JoaoFilipeResende/Master-Thesis/Mechanical Parts/cilider_camara.SLDPRT

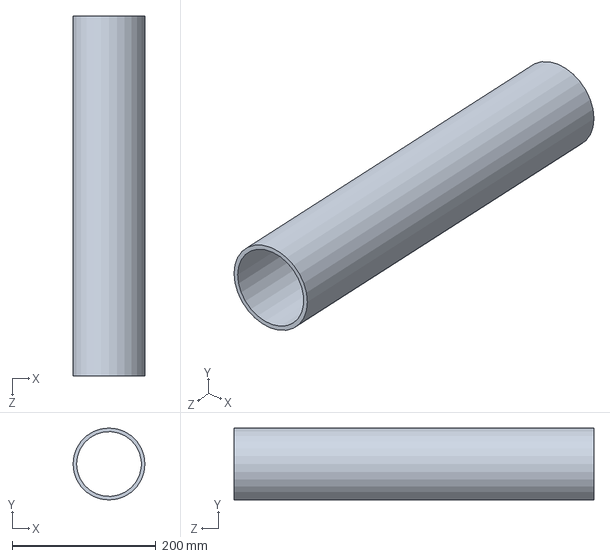
[picture p30: CAD file, 2022-01-28]
Mechanical Parts/cilider_camara.SLDPRT
100.0 x 100.0 x 500.0 mm
