JoaoFilipeResende/Master-Thesis/Mechanical Parts/tampa_back_camara.SLDPRT

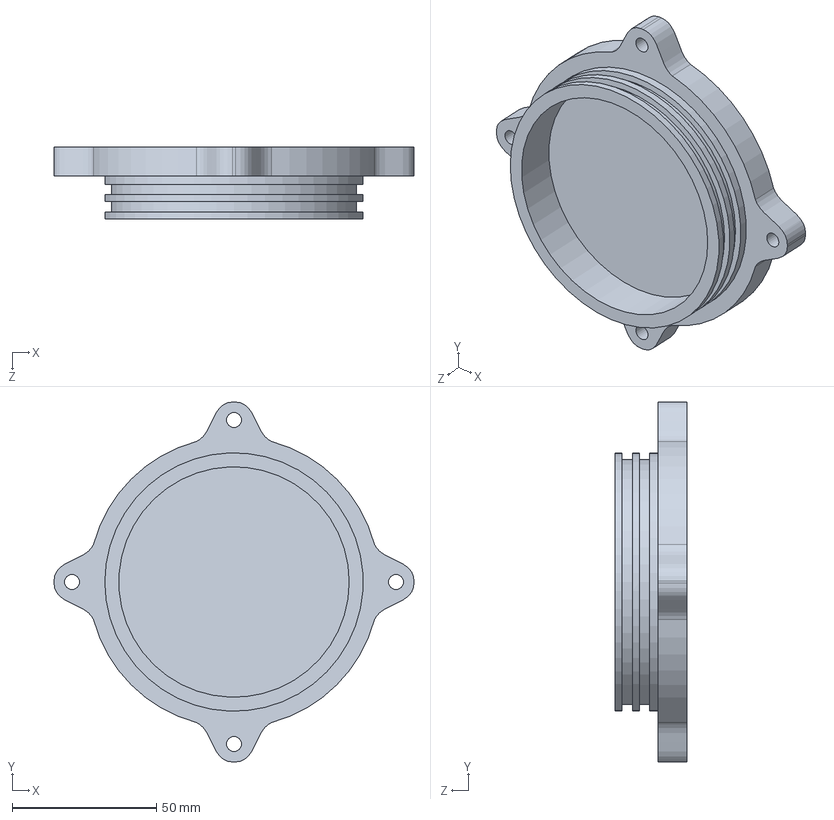
[picture p31: CAD file, 2022-01-28]
Mechanical Parts/tampa_back_camara.SLDPRT
125.0 x 125.0 x 25.0 mm
