JoaoFilipeResende/Master-Thesis/Mechanical Parts/mcbh8f-wb.SLDPRT

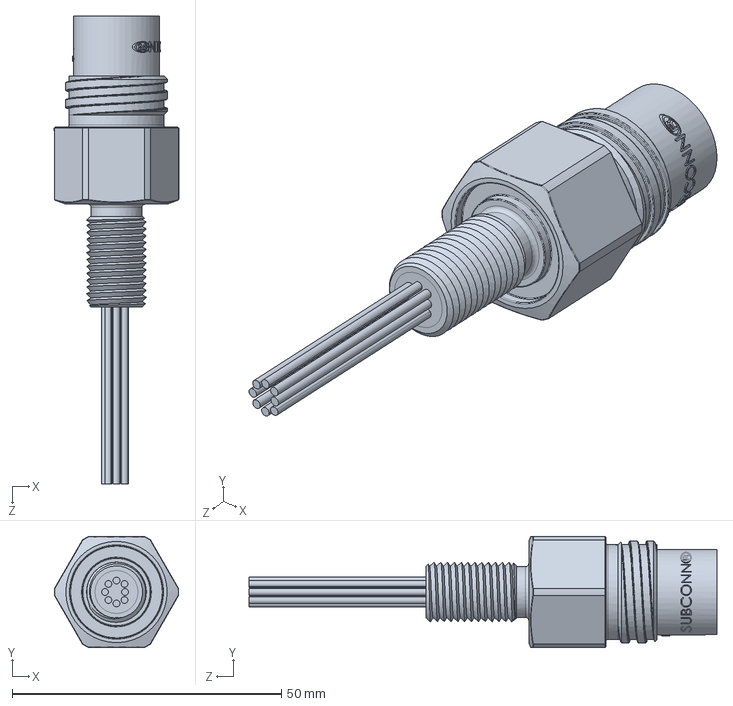
[picture p32: CAD file, 2022-01-28]
Mechanical Parts/mcbh8f-wb.SLDPRT
23.1 x 20.6 x 86.9 mm
