JoaoFilipeResende/Master-Thesis/Mechanical Parts/espacador.SLDPRT

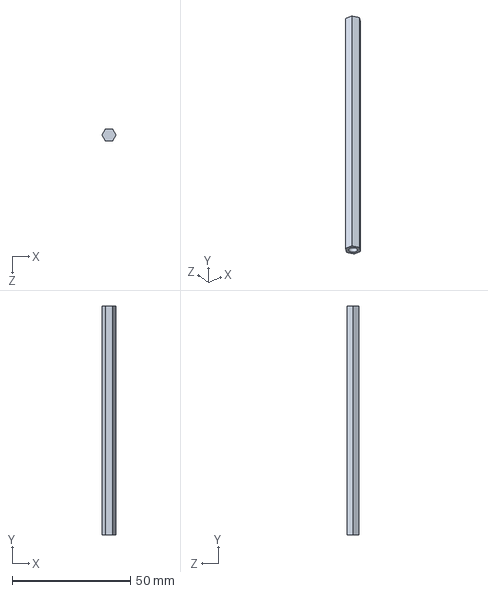
[picture p33: CAD file, 2022-01-28]
Mechanical Parts/espacador.SLDPRT
6.00 x 97.0 x 5.20 mm
