JoaoFilipeResende/Master-Thesis/Mechanical Parts/espacador_2.SLDPRT

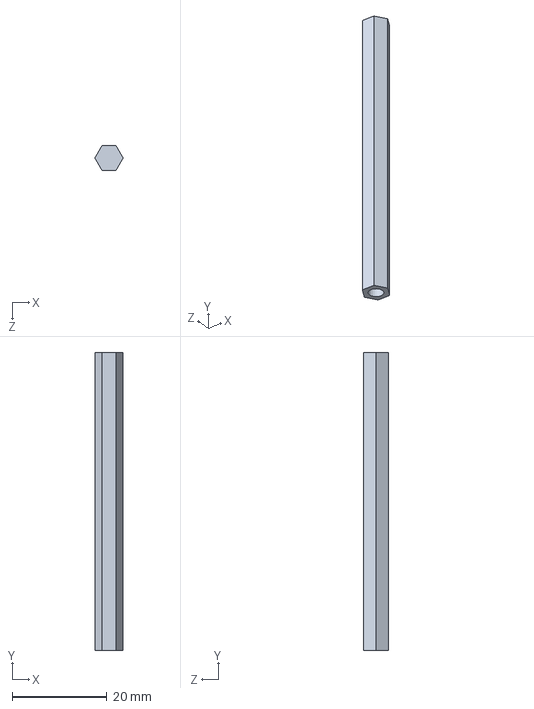
[picture p34: CAD file, 2022-01-28]
Mechanical Parts/espacador_2.SLDPRT
6.00 x 63.0 x 5.20 mm
