JoaoFilipeResende/Master-Thesis/Mechanical Parts/DTCM230-36.SLDPRT

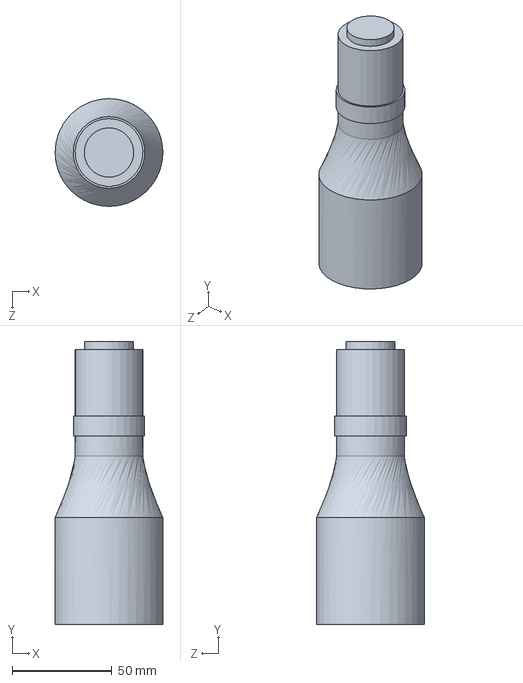
[picture p35: CAD file, 2022-01-28]
Mechanical Parts/DTCM230-36.SLDPRT
54.0 x 141.9 x 54.0 mm
