JoaoFilipeResende/Master-Thesis/Mechanical Parts/camara.SLDPRT

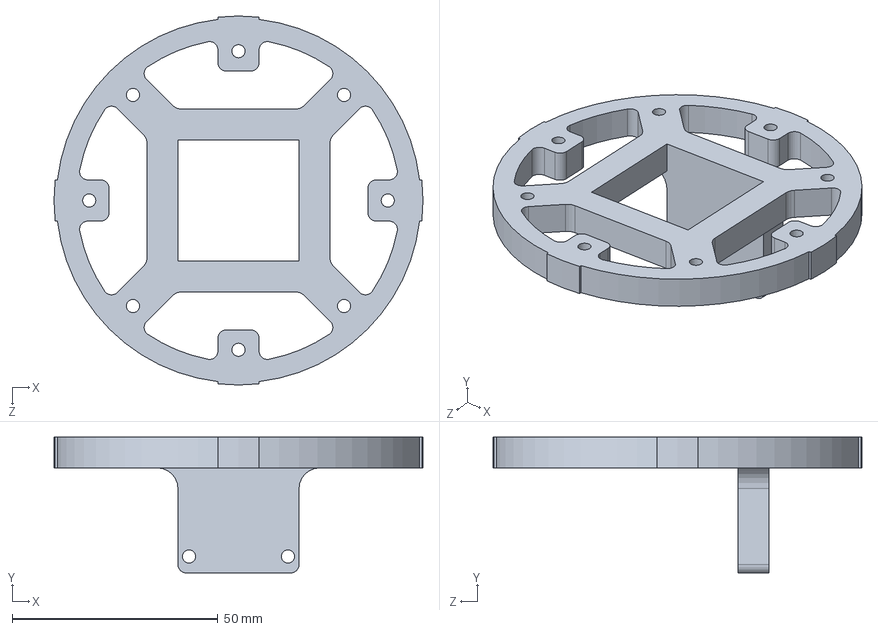
[picture p36: CAD file, 2022-01-28]
Mechanical Parts/camara.SLDPRT
89.6 x 33.0 x 89.6 mm
