JoaoFilipeResende/Master-Thesis/Mechanical Parts/suporte_lente_meio.SLDPRT

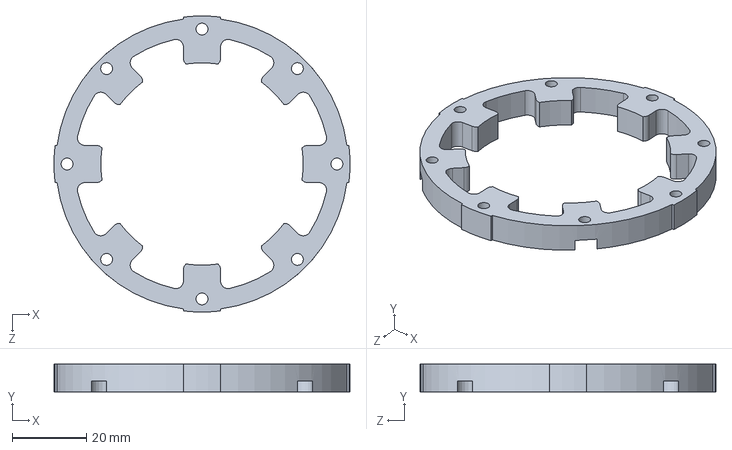
[picture p37: CAD file, 2022-01-28]
Mechanical Parts/suporte_lente_meio.SLDPRT
79.5 x 7.50 x 79.5 mm
