JoaoFilipeResende/Master-Thesis/Mechanical Parts/vara_suporte_camara.SLDPRT

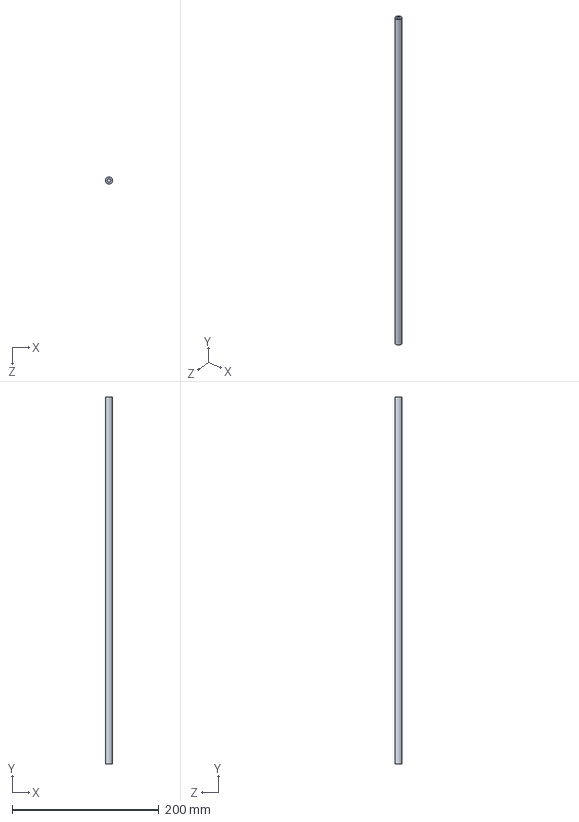
[picture p38: CAD file, 2022-01-28]
Mechanical Parts/vara_suporte_camara.SLDPRT
10.0 x 500.0 x 10.0 mm
