JoaoFilipeResende/Master-Thesis/Mechanical Parts/battery_sup.SLDPRT

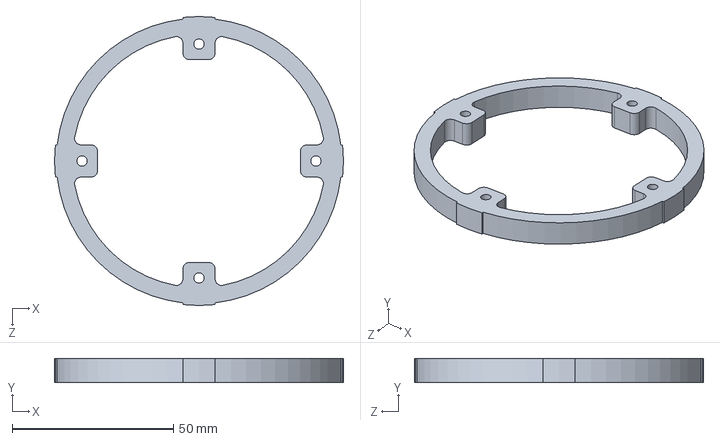
[picture p39: CAD file, 2022-01-28]
Mechanical Parts/battery_sup.SLDPRT
89.6 x 7.50 x 89.6 mm
