JoaoFilipeResende/Master-Thesis/Mechanical Parts/meio.SLDPRT

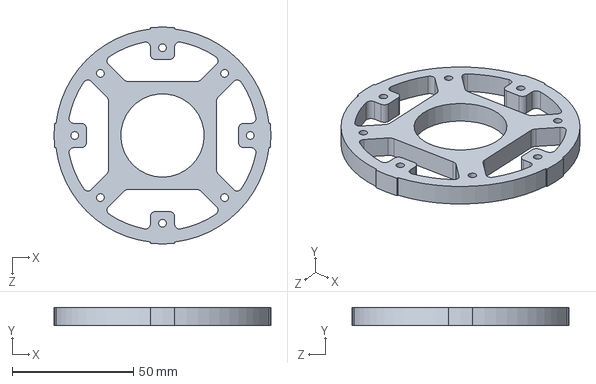
[picture p40: CAD file, 2022-01-28]
Mechanical Parts/meio.SLDPRT
89.6 x 7.50 x 89.6 mm
