JoaoFilipeResende/Master-Thesis/Mechanical Parts/tampa_front2_camara_light.SLDPRT

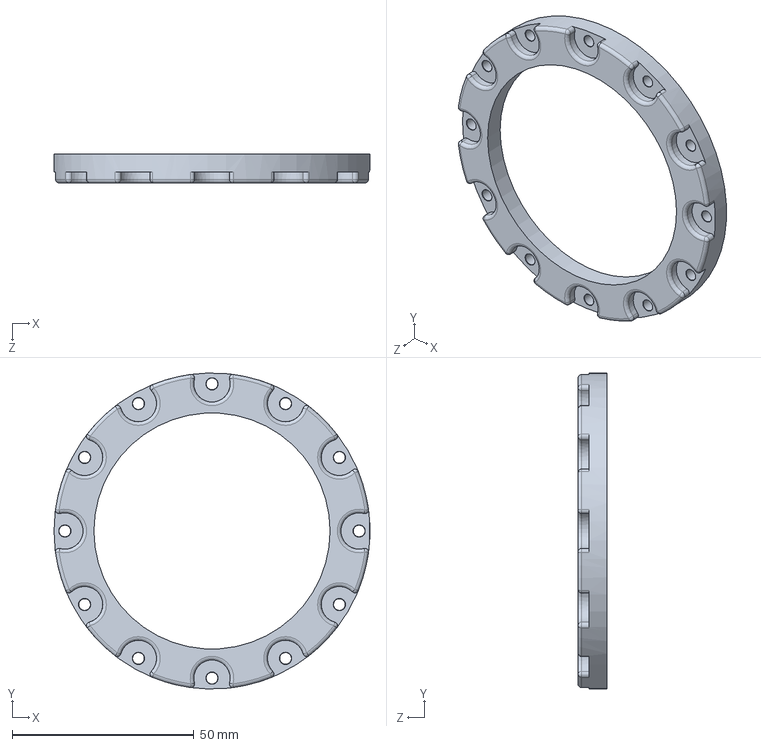
[picture p41: CAD file, 2022-01-28]
Mechanical Parts/tampa_front2_camara_light.SLDPRT
87.0 x 87.0 x 8.00 mm
