JoaoFilipeResende/Master-Thesis/Mechanical Parts/odroid.SLDPRT

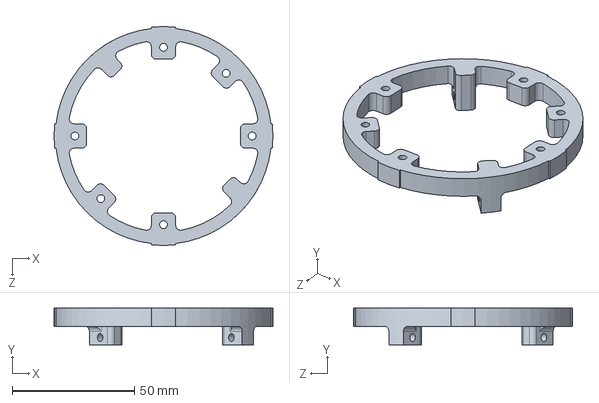
[picture p42: CAD file, 2022-01-28]
Mechanical Parts/odroid.SLDPRT
89.6 x 15.0 x 89.6 mm
