JoaoFilipeResende/Master-Thesis/Mechanical Parts/tampa_front1_camara_light.SLDPRT

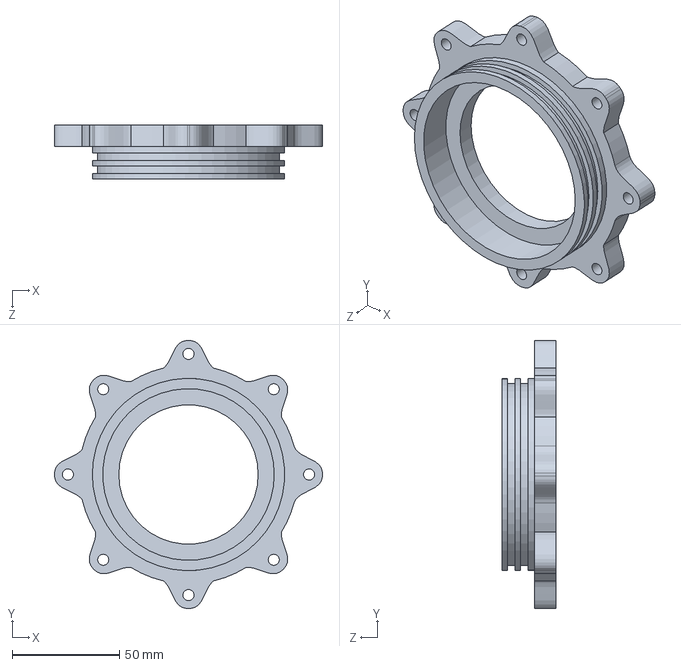
[picture p43: CAD file, 2022-01-28]
Mechanical Parts/tampa_front1_camara_light.SLDPRT
125.0 x 125.0 x 25.0 mm
