JoaoFilipeResende/Master-Thesis/Mechanical Parts/mcbh8m-wb.SLDPRT

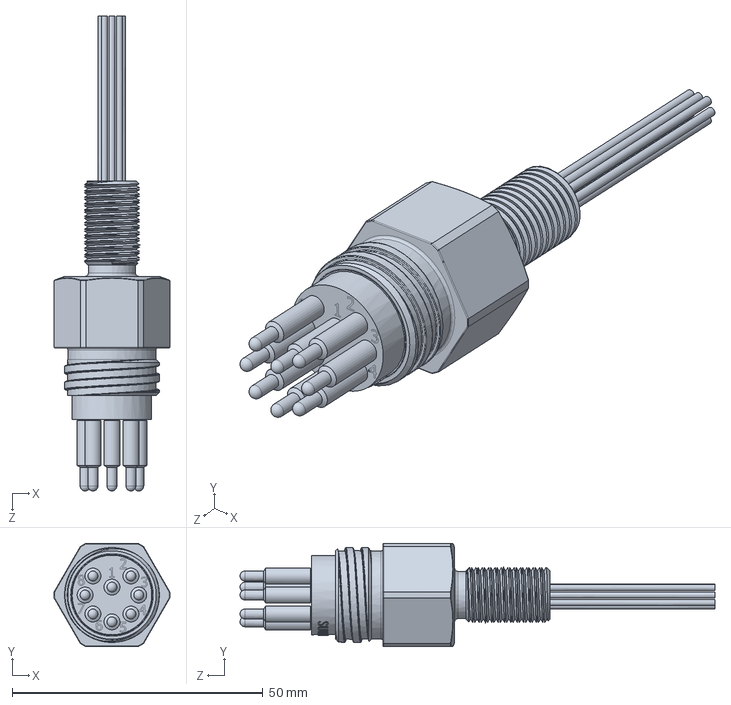
[picture p44: CAD file, 2022-01-28]
Mechanical Parts/mcbh8m-wb.SLDPRT
23.1 x 20.6 x 94.8 mm
