JoaoFilipeResende/Master-Thesis/Mechanical Parts/vara_suporte_setup.SLDPRT

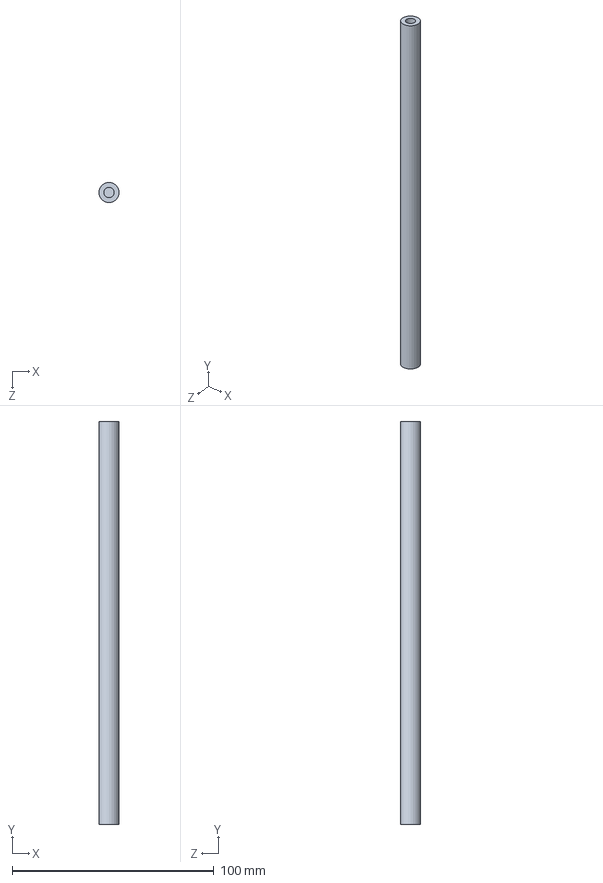
[picture p45: CAD file, 2022-01-28]
Mechanical Parts/vara_suporte_setup.SLDPRT
10.0 x 200.0 x 10.0 mm
