JoaoFilipeResende/Master-Thesis/Pictures/Results/f10.png

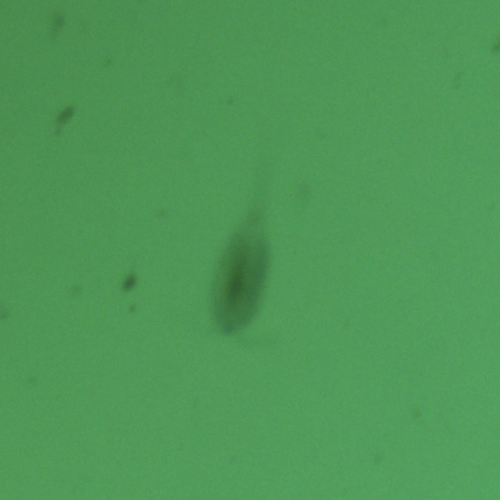
Pictures/Results/f10.png
