JoaoFilipeResende/Master-Thesis/Pictures/Results/f11.png

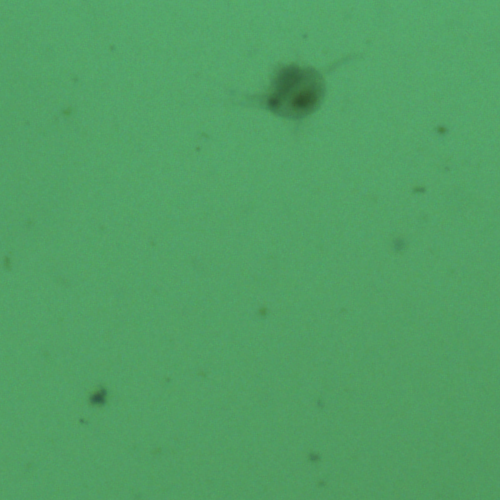
Pictures/Results/f11.png
