JoaoFilipeResende/Master-Thesis/Pictures/Results/f12.png

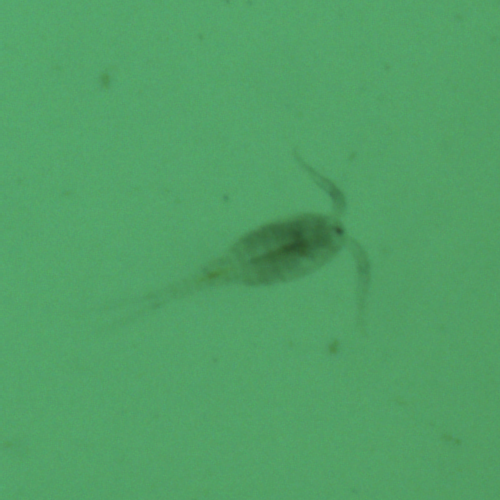
Pictures/Results/f12.png
