JoaoFilipeResende/Master-Thesis/Pictures/Results/f13.png

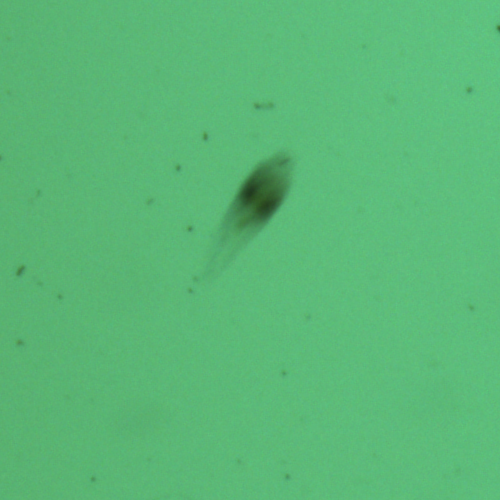
Pictures/Results/f13.png
