JoaoFilipeResende/Master-Thesis/Pictures/Results/f14.png

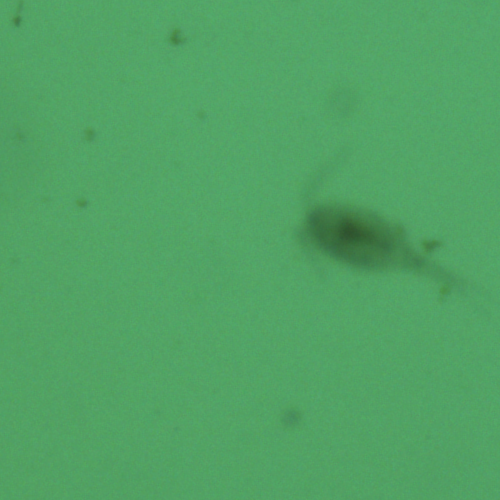
Pictures/Results/f14.png
