JoaoFilipeResende/Master-Thesis/Pictures/Results/f15.png

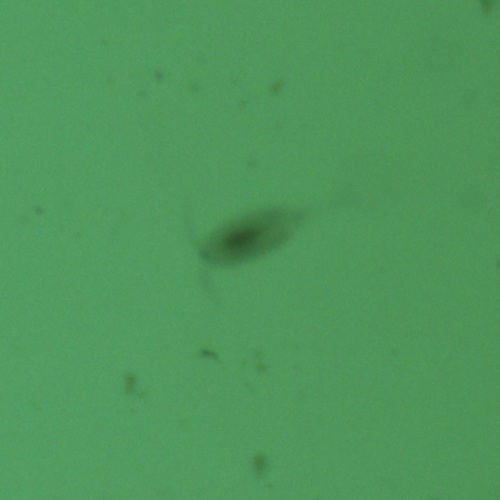
Pictures/Results/f15.png
