JoaoFilipeResende/Master-Thesis/Pictures/Results/f16.png

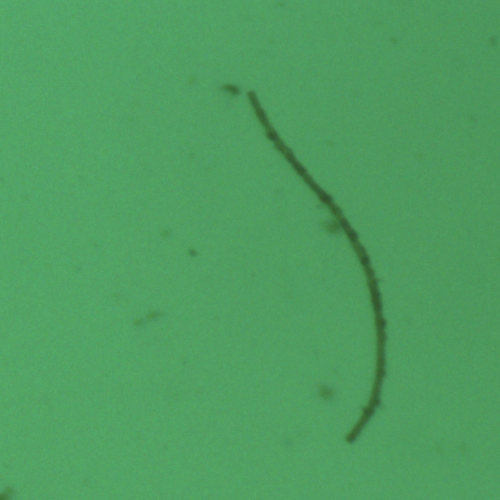
Pictures/Results/f16.png
